godiva-frappuccino/Debris/images/2c290cdd015fab251038b962eadfdfb8_preview_featured.jpg

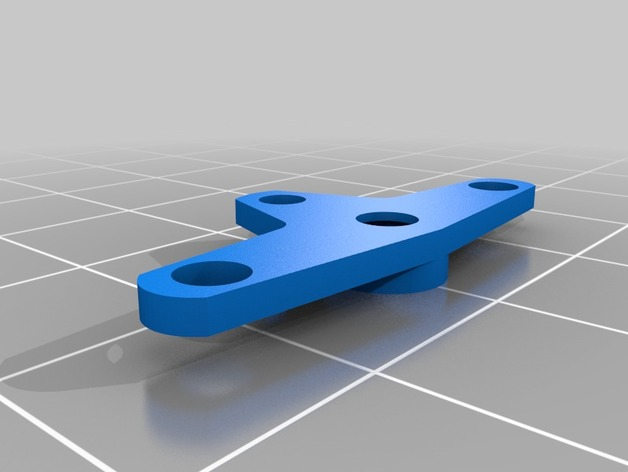
images/2c290cdd015fab251038b962eadfdfb8_preview_featured.jpg
