godiva-frappuccino/Debris/images/2e36dce3a7e96ff40d60458d7d626d25_preview_featured.jpg

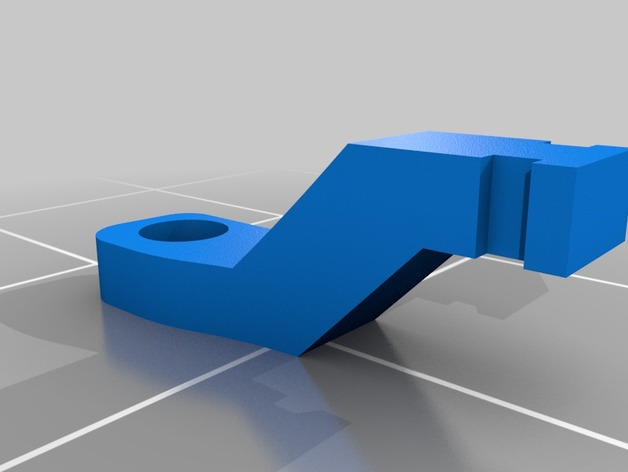
images/2e36dce3a7e96ff40d60458d7d626d25_preview_featured.jpg
