godiva-frappuccino/Debris/images/3e643964221fc305074e499954ee8910_preview_featured.jpg

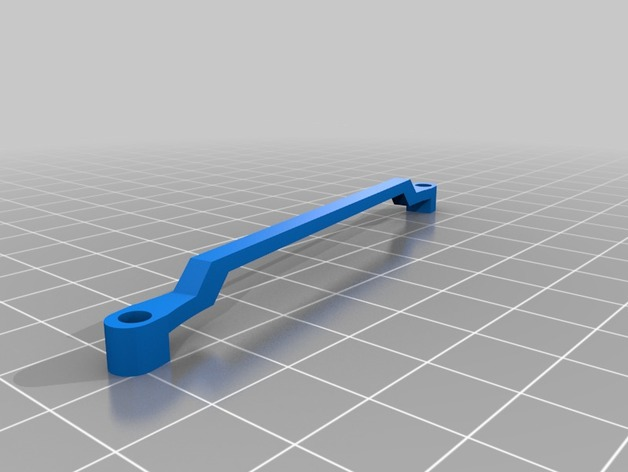
images/3e643964221fc305074e499954ee8910_preview_featured.jpg
