godiva-frappuccino/Debris/images/742a3c511cefb916380f659bb1ed0fe3_preview_featured.jpg

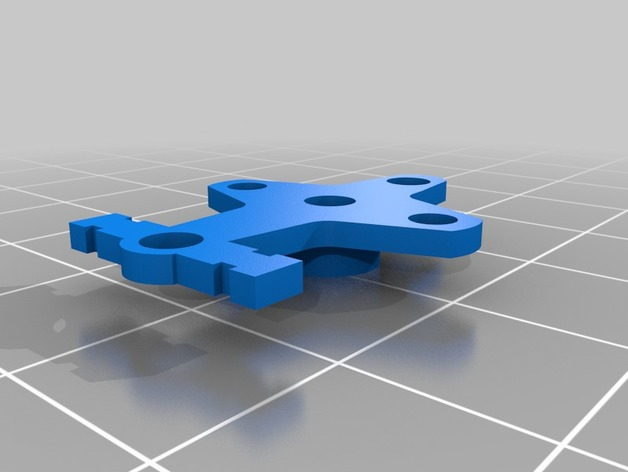
images/742a3c511cefb916380f659bb1ed0fe3_preview_featured.jpg
