godiva-frappuccino/Debris/images/abd0fb8388a870a47dae746e9b5bb497_preview_featured.jpg

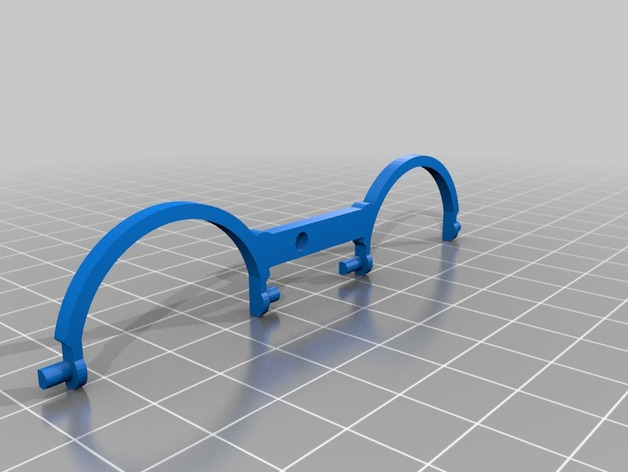
images/abd0fb8388a870a47dae746e9b5bb497_preview_featured.jpg
