godiva-frappuccino/Debris/images/b264a94abd4d63f7e08f6069fd6b144c_preview_featured.jpg

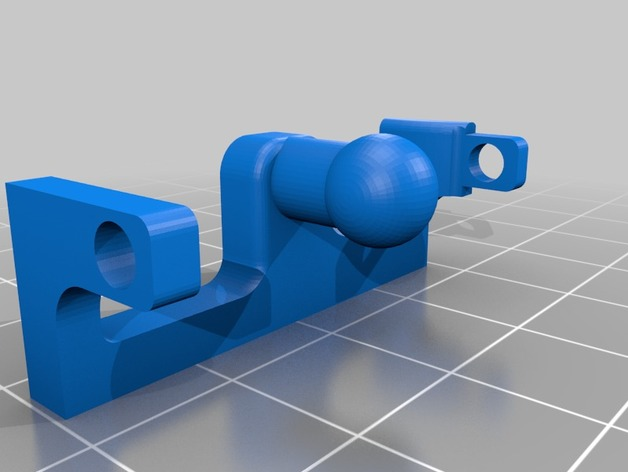
images/b264a94abd4d63f7e08f6069fd6b144c_preview_featured.jpg
