godiva-frappuccino/Debris/images/d2c5eb4723626bea9a90e39e4cc0381e_preview_featured.jpg

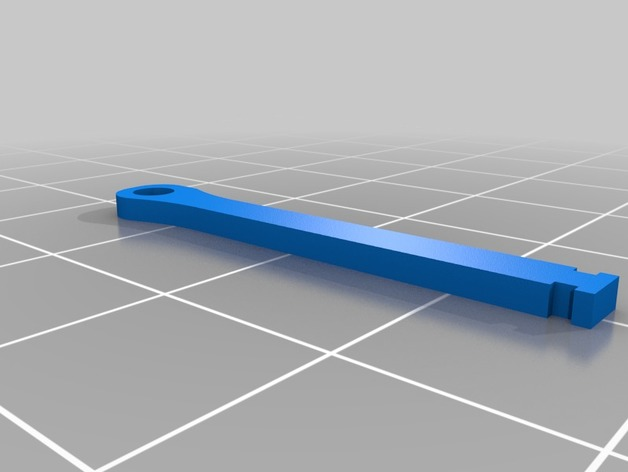
images/d2c5eb4723626bea9a90e39e4cc0381e_preview_featured.jpg
