godiva-frappuccino/Debris/images/d7e2e144c3d31e6a3746ac4350a4bf42_preview_featured.jpg

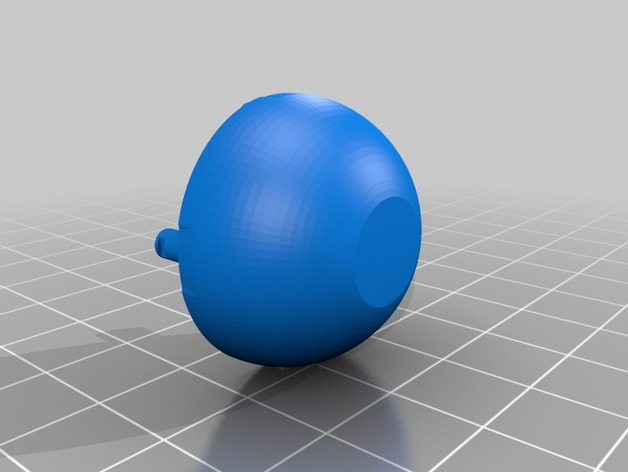
images/d7e2e144c3d31e6a3746ac4350a4bf42_preview_featured.jpg
