godiva-frappuccino/Debris/images/ed446c6b31eb5ddda6fec1828828eb2a_preview_featured.jpg

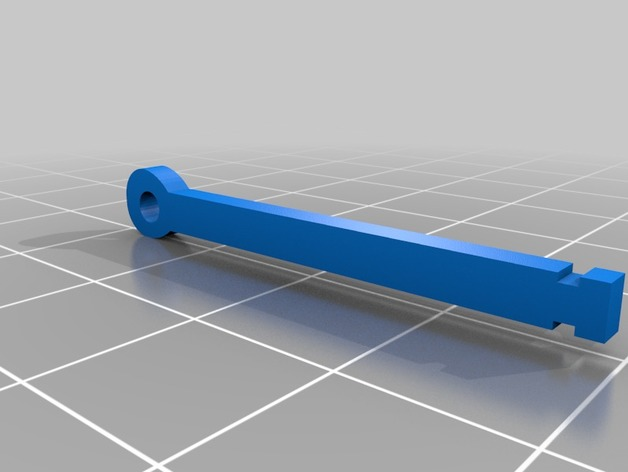
images/ed446c6b31eb5ddda6fec1828828eb2a_preview_featured.jpg
