godiva-frappuccino/Debris/images/efe24a7aafa8b2d56198f54efec4dd9e_preview_featured.jpg

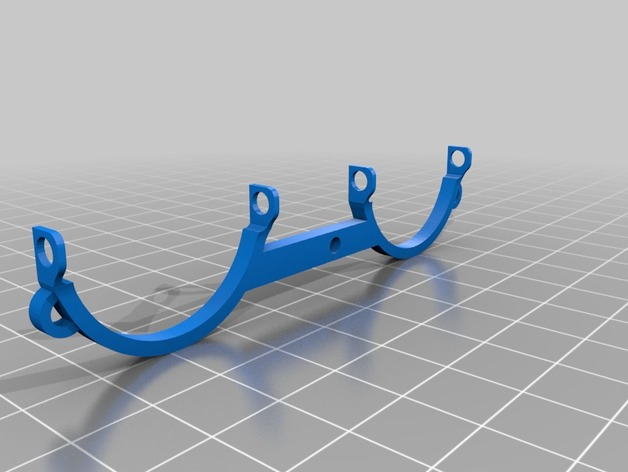
images/efe24a7aafa8b2d56198f54efec4dd9e_preview_featured.jpg
